westerlymerlin/RPi-XY-Controller/raspberry-pi/home/pi/ADCPi.py

#!/usr/bin/env python

"""
================================================
AB Electronics UK ADC Pi 8-Channel ADC

Requires smbus2 or python smbus to be installed
================================================
"""
from __future__ import absolute_import, division, print_function, \
    unicode_literals

try:
    from smbus2 import SMBus
except ImportError:
    try:
        from smbus import SMBus
    except ImportError:
        raise ImportError("python-smbus or smbus2 not found")
import re
import platform
import time


class Error(Exception):
    """Base class for exceptions in this module."""
    pass


class TimeoutError(Error):
    """The operation exceeded the given deadline."""
    pass


class ADCPi(object):
    """
    Control the MCP3424 ADC on the ADC Pi Plus and ADC Pi Zero
    """
    # internal variables
    __adc1_address = 0x68
    __adc2_address = 0x69

    __adc1_conf = 0x9C
    __adc2_conf = 0x9C

    __adc1_channel = 0x01
    __adc2_channel = 0x01

    __bitrate = 18  # current bitrate
    __conversionmode = 1  # Conversion Mode
    __pga = float(0.5)  # current PGA setting
    __lsb = float(0.0000078125)  # default LSB value for 18 bit
    __signbit = 0  # stores the sign bit for the sampled value

    # create a byte array and fill it with initial values to define the size
    __adcreading = bytearray([0, 0, 0, 0])

    __bus = None

    # local methods

    @staticmethod
    def __get_smbus(bus):
        """
        Internal method for getting an instance of the i2c bus

        :param bus: I2C bus number.  If the value is None the class will
                    try to find the i2c bus automatically using the device name
        :type bus: int
        :return: i2c bus for the target device
        :rtype: SMBus
        :raises IOError: Could not open the i2c bus
        """
        i2c__bus = 1
        if bus is not None:
            i2c__bus = bus
        else:
            # detect the device that is being used
            device = platform.uname()[1]

            if device == "orangepione":  # orange pi one
                i2c__bus = 0

            elif device == "orangepizero2":  # orange pi zero 2
                i2c__bus = 3

            elif device == "orangepiplus":  # orange pi plus
                i2c__bus = 0

            elif device == "orangepipcplus":  # orange pi pc plus
                i2c__bus = 0

            elif device == "linaro-alip":  # Asus Tinker Board
                i2c__bus = 1

            elif device == "bpi-m2z":  # Banana Pi BPI M2 Zero Ubuntu
                i2c__bus = 0

            elif device == "bpi-iot-ros-ai":  # Banana Pi BPI M2 Zero Raspbian
                i2c__bus = 0

            elif device == "raspberrypi":  # running on raspberry pi
                # detect i2C port number and assign to i2c__bus
                for line in open('/proc/cpuinfo').readlines():
                    model = re.match('(.*?)\\s*:\\s*(.*)', line)
                    if model:
                        (name, value) = (model.group(1), model.group(2))
                        if name == "Revision":
                            if value[-4:] in ('0002', '0003'):
                                i2c__bus = 0  # original model A or B
                            else:
                                i2c__bus = 1  # later models
                            break
        try:
            return SMBus(i2c__bus)
        except FileNotFoundError:
            raise FileNotFoundError("Bus not found.  Check that you have selected the correct I2C bus.")
        except OSError as err:
            raise ("OS error: {0}".format(err))
        except IOError as err:
            raise ("IO error: {0}".format(err))
        except Exception as err:
            raise err

    def __updatebyte(self, byte, mask, value):
        """
        Internal method for setting the value of a single bit within a byte

        :param byte: input value
        :type byte: int
        :param mask: location to update
        :type mask: int
        :param value: new bit, 0 or 1
        :type value: int
        :return: updated value
        :rtype: int
        """
        byte &= mask
        byte |= value
        return byte

    def __setchannel(self, channel):
        """
        Internal method for updating the config to the selected channel

        :param channel: selected channel
        :type channel: int
        :raises ValueError: __setchannel: channel out of range 1 to 8
        """
        if channel >= 1 and channel <= 4:
            if channel != self.__adc1_channel:
                self.__adc1_channel = channel
                if channel == 1:  # bit 5 = 1, bit 6 = 0
                    self.__adc1_conf = self.__updatebyte(self.__adc1_conf,
                                                         0x9F, 0x00)
                elif channel == 2:  # bit 5 = 1, bit 6 = 0
                    self.__adc1_conf = self.__updatebyte(self.__adc1_conf,
                                                         0x9F, 0x20)
                elif channel == 3:  # bit 5 = 0, bit 6 = 1
                    self.__adc1_conf = self.__updatebyte(self.__adc1_conf,
                                                         0x9F, 0x40)
                elif channel == 4:  # bit 5 = 1, bit 6 = 1
                    self.__adc1_conf = self.__updatebyte(self.__adc1_conf,
                                                         0x9F, 0x60)
        elif channel >= 5 and channel <= 8:
            if channel != self.__adc2_channel:
                self.__adc2_channel = channel
                if channel == 5:  # bit 5 = 1, bit 6 = 0
                    self.__adc2_conf = self.__updatebyte(self.__adc2_conf,
                                                         0x9F, 0x00)
                elif channel == 6:  # bit 5 = 1, bit 6 = 0
                    self.__adc2_conf = self.__updatebyte(self.__adc2_conf,
                                                         0x9F, 0x20)
                elif channel == 7:  # bit 5 = 0, bit 6 = 1
                    self.__adc2_conf = self.__updatebyte(self.__adc2_conf,
                                                         0x9F, 0x40)
                elif channel == 8:  # bit 5 = 1, bit 6 = 1
                    self.__adc2_conf = self.__updatebyte(self.__adc2_conf,
                                                         0x9F, 0x60)
        else:
            raise ValueError('__setchannel: channel out of range 1 to 8')
        return

    # init object with i2caddress, default is 0x68, 0x69 for ADCPi board
    def __init__(self, address=0x68, address2=0x69, rate=18, bus=None):
        """
        Class constructor - Initialise the two ADC chips with their
        I2C addresses and bit rate.

        :param address: I2C address for channels 1 to 4, defaults to 0x68
        :type address: int, optional
        :raises ValueError: address out of range 0x68 to 0x6F
        :param address2: I2C address for channels 5 to 8, defaults to 0x69
        :type address2: int, optional
        :raises ValueError: address2 out of range 0x68 to 0x6F
        :param rate: bit rate, defaults to 18
        :type rate: int, optional
        :param bus: I2C bus number.  If no value is set the class will try to
                    find the i2c bus automatically using the device name
        :type bus: int, optional
        """
        self.__bus = self.__get_smbus(bus)
        if address >= 0x68 and address <= 0x6F:
            self.__adc1_address = address
        else:
            raise ValueError('address out of range 0x68 to 0x6F')

        if address2 >= 0x68 and address2 <= 0x6F:
            self.__adc2_address = address2
        else:
            raise ValueError('address2 out of range 0x68 to 0x6F')
        self.set_bit_rate(rate)

    def set_i2c_address1(self, address):
        """
        Set the I2C address for the ADC on channels 1 to 4

        :param address: I2C address for channels 1 to 4, defaults to 0x68
        :type address: int, optional
        :raises ValueError: address out of range 0x68 to 0x6F
        """
        if address >= 0x68 and address <= 0x6F:
            self.__adc1_address = address
        else:
            raise ValueError('address out of range 0x68 to 0x6F')

    def set_i2caddress2(self, address):
        """
        Set the I2C address for the ADC on channels 5 to 8

        :param address: I2C address for channels 5 to 8, defaults to 0x68
        :type address: int, optional
        :raises ValueError: address out of range 0x68 to 0x6F
        """
        if address >= 0x68 and address <= 0x6F:
            self.__adc2_address = address
        else:
            raise ValueError('address out of range 0x68 to 0x6F')

    def get_i2c_address1(self):
        """
        Get the I2C address for the ADC on channels 1 to 4
        :return: I2C address
        :rtype: number
        """
        return self.__adc1_address

    def get_i2c_address2(self):
        """
        Get the I2C address for the ADC on channels 5 to 8
        :return: I2C address
        :rtype: number
        """
        return self.__adc2_address

    def read_voltage(self, channel):
        """
        Returns the voltage from the selected ADC channel

        :param channel: 1 to 8
        :type channel: int
        :raises ValueError: read_voltage: channel out of range (1 to 8 allowed)
        :return: voltage
        :rtype: float
        """
        if channel < 1 or channel > 8:
            raise ValueError('read_voltage: channel out of range (1 to 8 allowed)')

        raw = self.read_raw(channel)
        voltage = float(0.0)
        if not self.__signbit:
            voltage = float(
                (raw * (self.__lsb / self.__pga)) * 2.471)

        return voltage

    def read_raw(self, channel):
        """
        Reads the raw value from the selected ADC channel

        :param channel: 1 to 8
        :type channel: int
        :raises ValueError: read_raw: channel out of range
        :raises TimeoutError: read_raw: channel x conversion timed out
        :return: raw ADC output
        :rtype: int
        """
        if channel < 1 or channel > 8:
            raise ValueError('read_raw: channel out of range (1 to 8 allowed)')

        high = 0
        low = 0
        mid = 0
        cmdbyte = 0

        # get the config and i2c address for the selected channel
        self.__setchannel(channel)
        if channel <= 4:
            config = self.__adc1_conf
            address = self.__adc1_address
        else:
            config = self.__adc2_conf
            address = self.__adc2_address

        # if the conversion mode is set to one-shot update the ready bit to 1
        if self.__conversionmode == 0:
            config = config | (1 << 7)
            self.__bus.write_byte(address, config)
            config = config & ~(1 << 7)  # reset the ready bit to 0

        # determine a reasonable amount of time to wait for the conversion
        if self.__bitrate == 18:
            seconds_per_sample = 0.26666
        elif self.__bitrate == 16:
            seconds_per_sample = 0.06666
        elif self.__bitrate == 14:
            seconds_per_sample = 0.01666
        elif self.__bitrate == 12:
            seconds_per_sample = 0.00416
        timeout_time = time.monotonic() + (100 * seconds_per_sample)

        # keep reading the ADC data until the conversion result is ready
        while True:
            __adcreading = self.__bus.read_i2c_block_data(address, config, 4)
            if self.__bitrate == 18:
                high = __adcreading[0]
                mid = __adcreading[1]
                low = __adcreading[2]
                cmdbyte = __adcreading[3]
            else:
                high = __adcreading[0]
                mid = __adcreading[1]
                cmdbyte = __adcreading[2]
            # check if bit 7 of the command byte is 0.
            if (cmdbyte & (1 << 7)) == 0:
                break
            elif time.monotonic() > timeout_time:
                msg = 'read_raw: channel %i conversion timed out' % channel
                raise TimeoutError(msg)
            else:
                time.sleep(0.00001)  # sleep for 10 microseconds

        self.__signbit = False
        raw = 0
        # extract the returned bytes and combine them in the correct order
        if self.__bitrate == 18:
            raw = ((high & 0x03) << 16) | (mid << 8) | low
            self.__signbit = bool(raw & (1 << 17))
            raw = raw & ~(1 << 17)  # reset sign bit to 0

        elif self.__bitrate == 16:
            raw = (high << 8) | mid
            self.__signbit = bool(raw & (1 << 15))
            raw = raw & ~(1 << 15)  # reset sign bit to 0

        elif self.__bitrate == 14:
            raw = ((high & 0b00111111) << 8) | mid
            self.__signbit = bool(raw & (1 << 13))
            raw = raw & ~(1 << 13)  # reset sign bit to 0

        elif self.__bitrate == 12:
            raw = ((high & 0x0f) << 8) | mid
            self.__signbit = bool(raw & (1 << 11))
            raw = raw & ~(1 << 11)  # reset sign bit to 0

        return raw

    def set_pga(self, gain):
        """
        PGA (programmable gain amplifier) gain selection

        :param gain: 1 = 1x
                     2 = 2x
                     4 = 4x
                     8 = 8x
        :type gain: int
        :raises ValueError: set_pga: gain out of range
        """

        if gain == 1:
            # bit 0 = 0, bit 1 = 0
            self.__adc1_conf = self.__updatebyte(self.__adc1_conf, 0xFC, 0x00)
            self.__adc2_conf = self.__updatebyte(self.__adc2_conf, 0xFC, 0x00)
            self.__pga = 0.5
        elif gain == 2:
            # bit 0 = 1, bit 1 = 0
            self.__adc1_conf = self.__updatebyte(self.__adc1_conf, 0xFC, 0x01)
            self.__adc2_conf = self.__updatebyte(self.__adc2_conf, 0xFC, 0x01)
            self.__pga = 1.0
        elif gain == 4:
            # bit 0 = 0, bit 1 = 1
            self.__adc1_conf = self.__updatebyte(self.__adc1_conf, 0xFC, 0x02)
            self.__adc2_conf = self.__updatebyte(self.__adc2_conf, 0xFC, 0x02)
            self.__pga = 2.0
        elif gain == 8:
            # bit 0 = 1, bit 1 = 1
            self.__adc1_conf = self.__updatebyte(self.__adc1_conf, 0xFC, 0x03)
            self.__adc2_conf = self.__updatebyte(self.__adc2_conf, 0xFC, 0x03)
            self.__pga = 4.0
        else:
            raise ValueError('set_pga: gain out of range')

        self.__bus.write_byte(self.__adc1_address, self.__adc1_conf)
        self.__bus.write_byte(self.__adc2_address, self.__adc2_conf)
        return

    def set_bit_rate(self, rate):
        """
        Sample rate and resolution

        :param rate: 12 = 12 bit (240SPS max)
                     14 = 14 bit (60SPS max)
                     16 = 16 bit (15SPS max)
                     18 = 18 bit (3.75SPS max)
        :type rate: int
        :raises ValueError: set_bit_rate: rate out of range
        """

        if rate == 12:
            # bit 2 = 0, bit 3 = 0
            self.__adc1_conf = self.__updatebyte(self.__adc1_conf, 0xF3, 0x00)
            self.__adc2_conf = self.__updatebyte(self.__adc2_conf, 0xF3, 0x00)
            self.__bitrate = 12
            self.__lsb = 0.0005
        elif rate == 14:
            # bit 2 = 1, bit 3 = 0
            self.__adc1_conf = self.__updatebyte(self.__adc1_conf, 0xF3, 0x04)
            self.__adc2_conf = self.__updatebyte(self.__adc2_conf, 0xF3, 0x04)
            self.__bitrate = 14
            self.__lsb = 0.000125
        elif rate == 16:
            # bit 2 = 0, bit 3 = 1
            self.__adc1_conf = self.__updatebyte(self.__adc1_conf, 0xF3, 0x08)
            self.__adc2_conf = self.__updatebyte(self.__adc2_conf, 0xF3, 0x08)
            self.__bitrate = 16
            self.__lsb = 0.00003125
        elif rate == 18:
            # bit 2 = 1, bit 3 = 1
            self.__adc1_conf = self.__updatebyte(self.__adc1_conf, 0xF3, 0x0C)
            self.__adc2_conf = self.__updatebyte(self.__adc2_conf, 0xF3, 0x0C)
            self.__bitrate = 18
            self.__lsb = 0.0000078125
        else:
            raise ValueError('set_bit_rate: rate out of range')

        self.__bus.write_byte(self.__adc1_address, self.__adc1_conf)
        self.__bus.write_byte(self.__adc2_address, self.__adc2_conf)
        return

    def set_conversion_mode(self, mode):
        """
        conversion mode for ADC

        :param mode: 0 = One shot conversion mode
                     1 = Continuous conversion mode
        :type mode: int
        :raises ValueError: set_conversion_mode: mode out of range
        """
        if mode == 0:
            # bit 4 = 0
            self.__adc1_conf = self.__updatebyte(self.__adc1_conf, 0xEF, 0x00)
            self.__adc2_conf = self.__updatebyte(self.__adc1_conf, 0xEF, 0x00)
            self.__conversionmode = 0
        elif mode == 1:
            # bit 4 = 1
            self.__adc1_conf = self.__updatebyte(self.__adc1_conf, 0xEF, 0x10)
            self.__adc2_conf = self.__updatebyte(self.__adc1_conf, 0xEF, 0x10)
            self.__conversionmode = 1
        else:
            raise ValueError('set_conversion_mode: mode out of range')

        return
